Skelebot/vgbd44/images/photos/leds-right.jpg

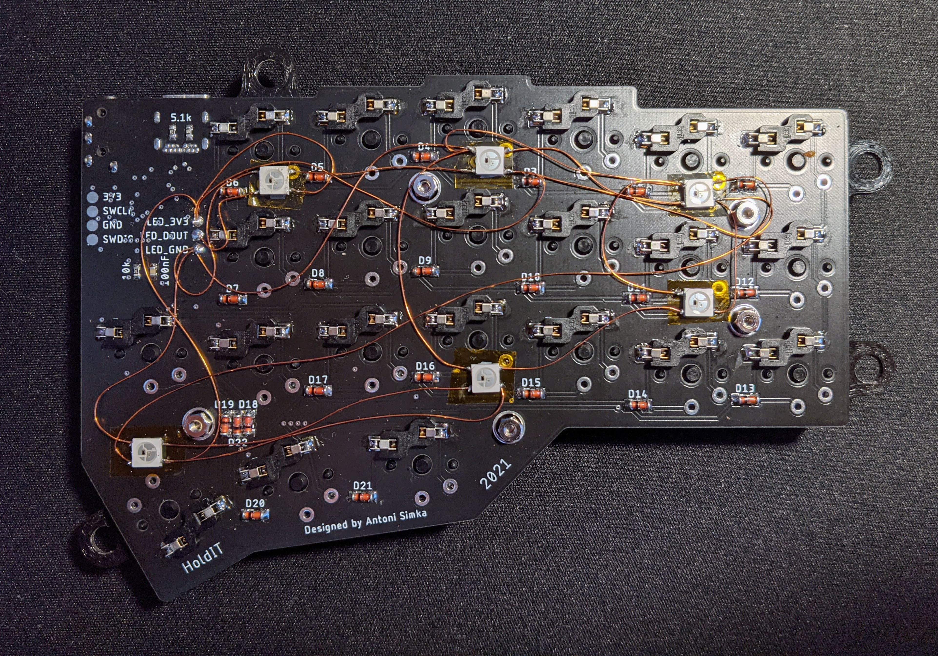
images/photos/leds-right.jpg
