Skelebot/vgbd44/images/photos/leds-working.jpg

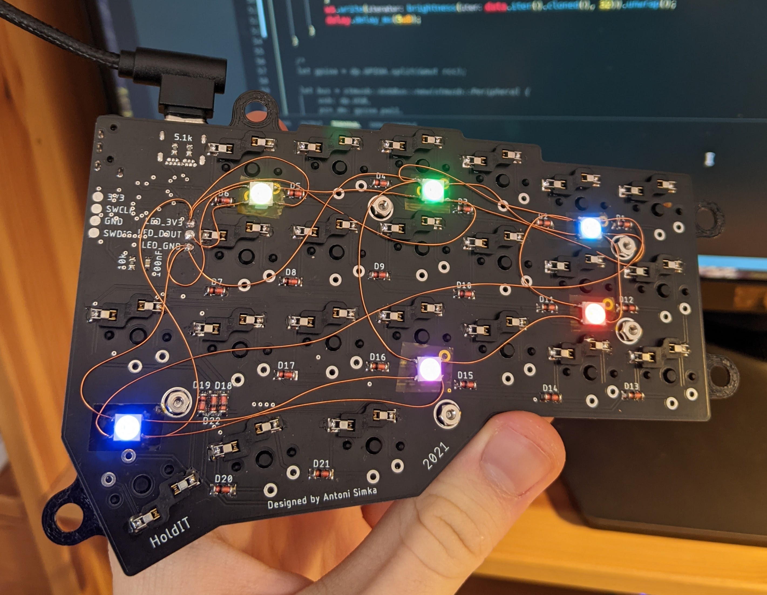
images/photos/leds-working.jpg
