Skelebot/vgbd44/images/renders/bottom-plate v6-front.png

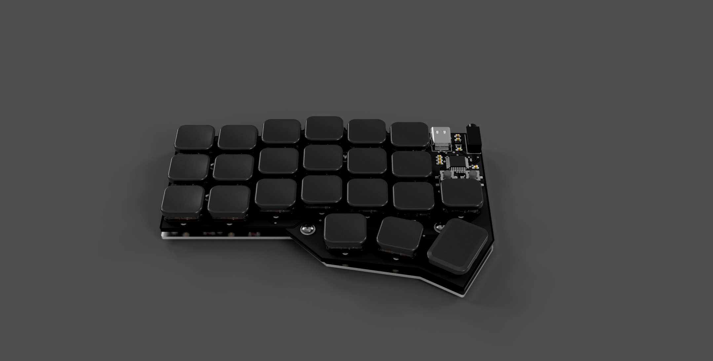
images/renders/bottom-plate v6-front.png
