Skelebot/vgbd44/images/renders/bottom-plate v6-rev.png

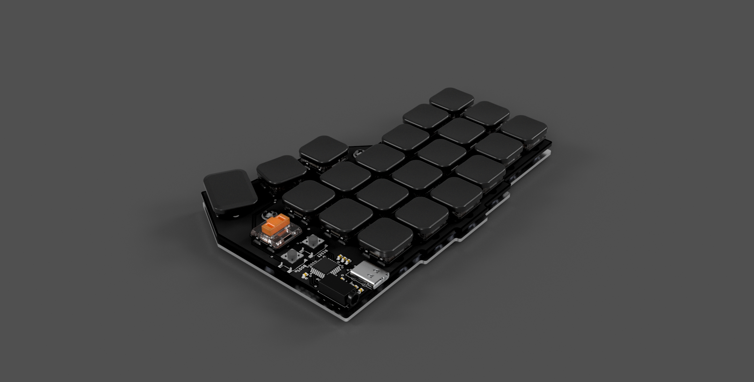
images/renders/bottom-plate v6-rev.png
