Skelebot/vgbd44/images/renders/bottom-plate v6.png

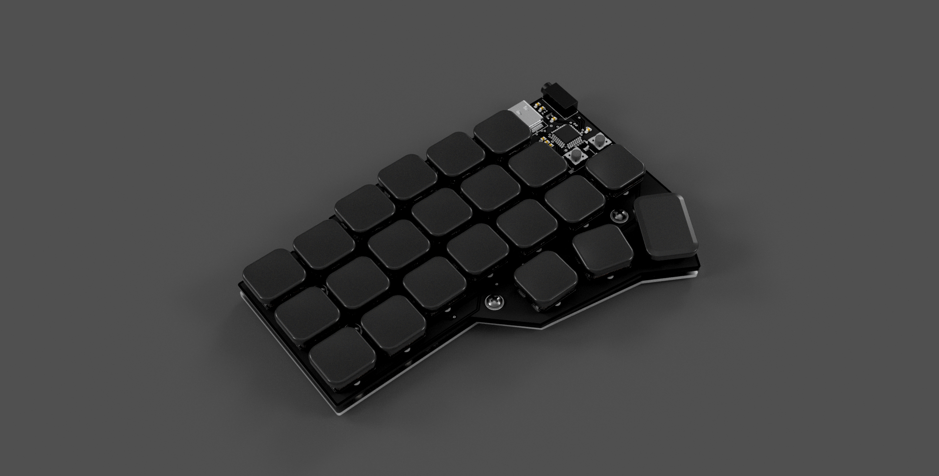
images/renders/bottom-plate v6.png
