Skelebot/vgbd44/images/renders/complete-left-top.png

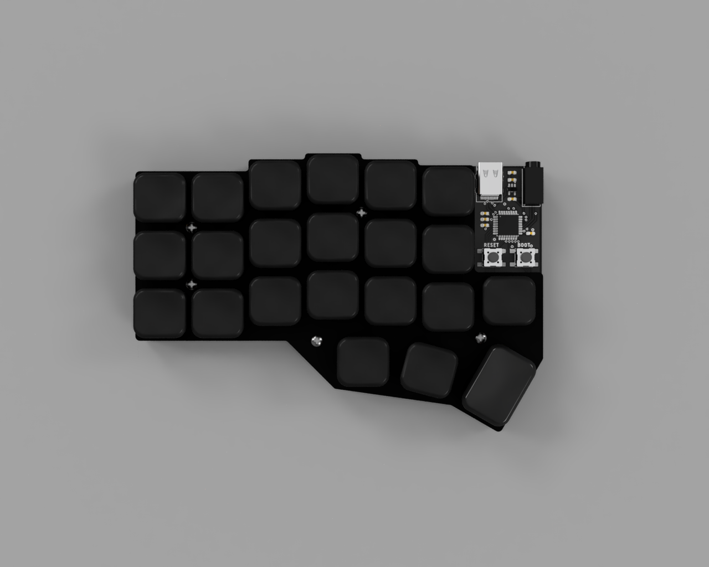
images/renders/complete-left-top.png
