Skelebot/vgbd44/images/renders/left v6.png

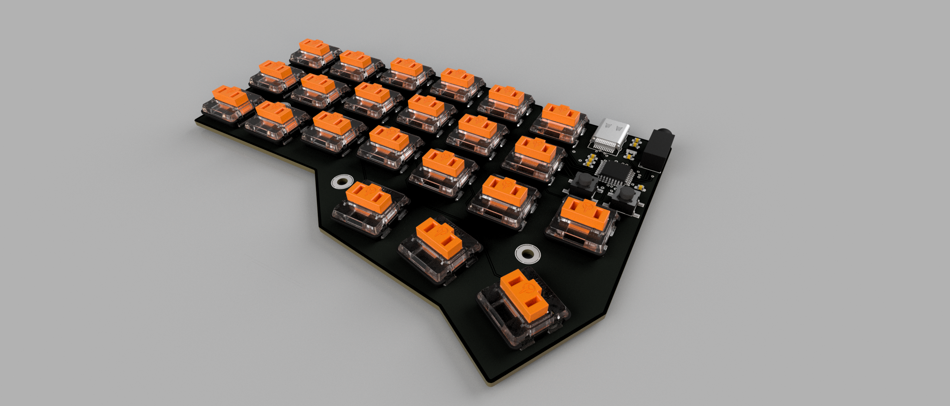
images/renders/left v6.png
